hitech95/X-Mas-WTree/3DModel/IMG_20201217_145501.jpg

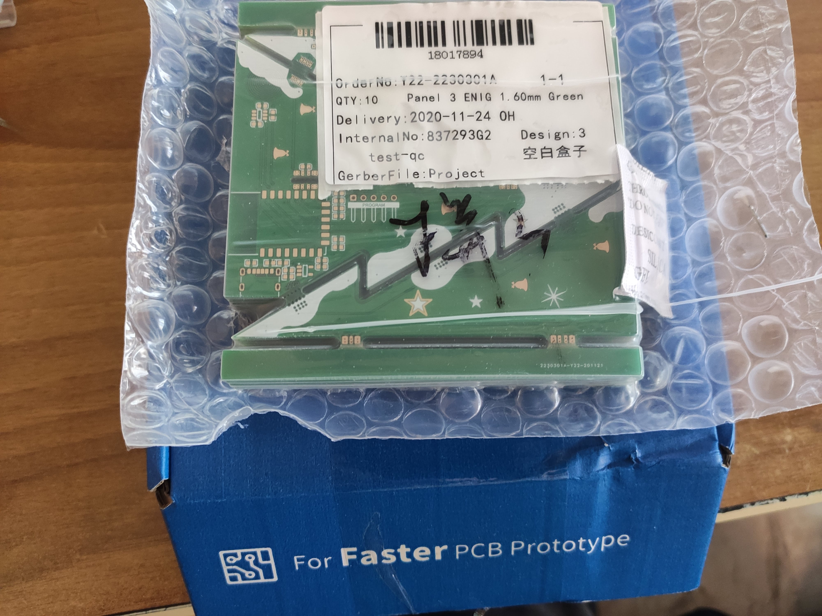
3DModel/IMG_20201217_145501.jpg
