hitech95/X-Mas-WTree/3DModel/IMG_20201217_232008.jpg

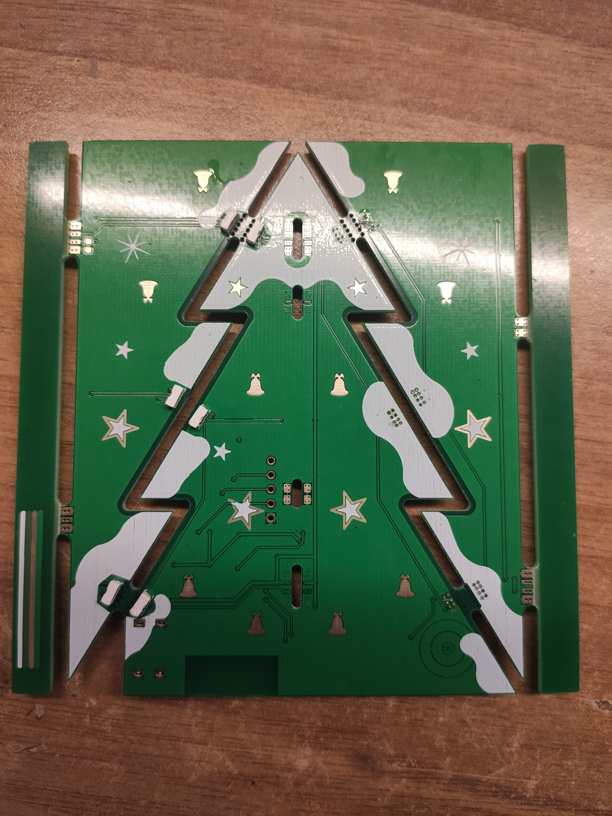
3DModel/IMG_20201217_232008.jpg
