hitech95/X-Mas-WTree/3DModel/IMG_20201218_164648.jpg

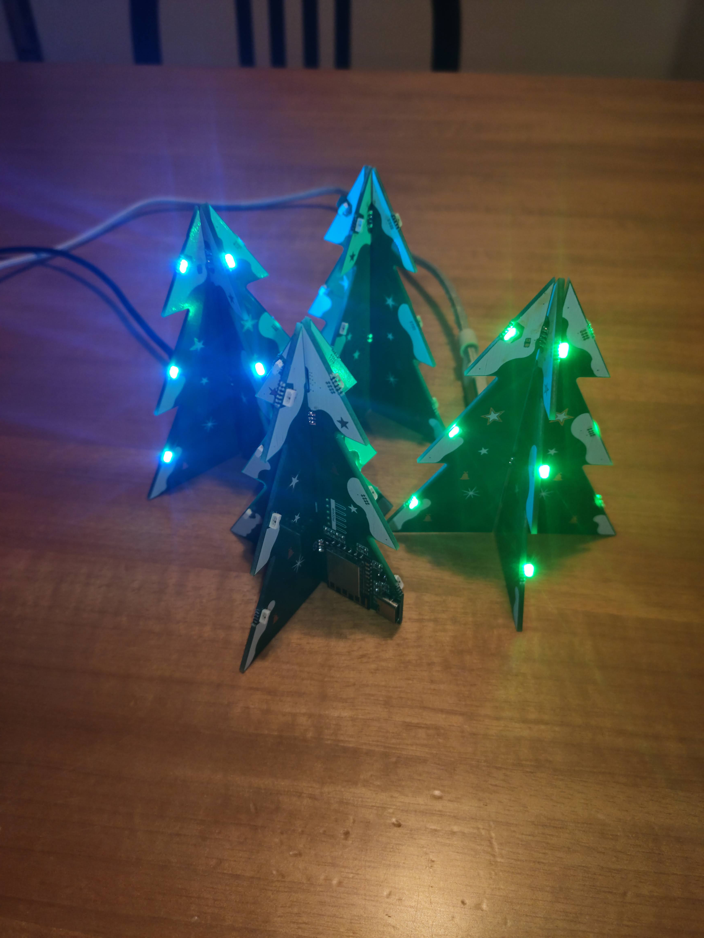
3DModel/IMG_20201218_164648.jpg
