hitech95/X-Mas-WTree/3DModel/IMG_20201217_232152.jpg

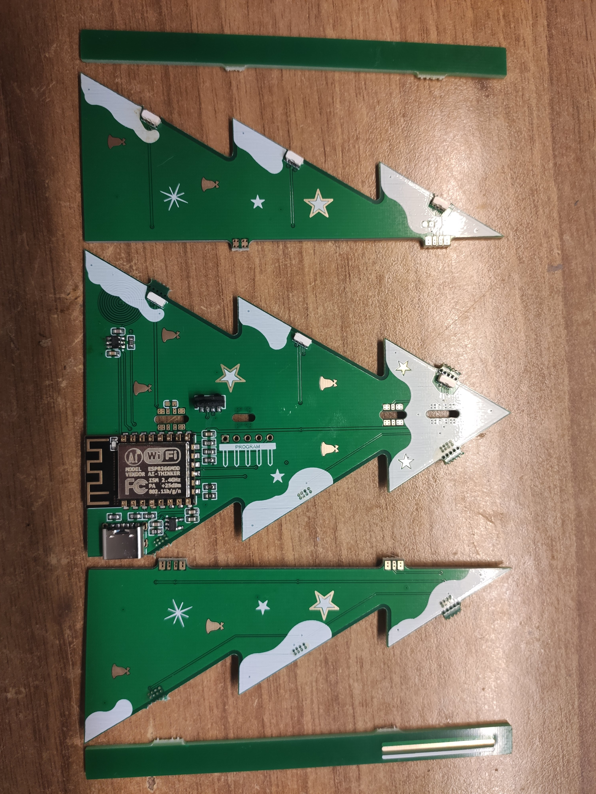
3DModel/IMG_20201217_232152.jpg
